NCAR/openiotwx/docs/img/architecture.png

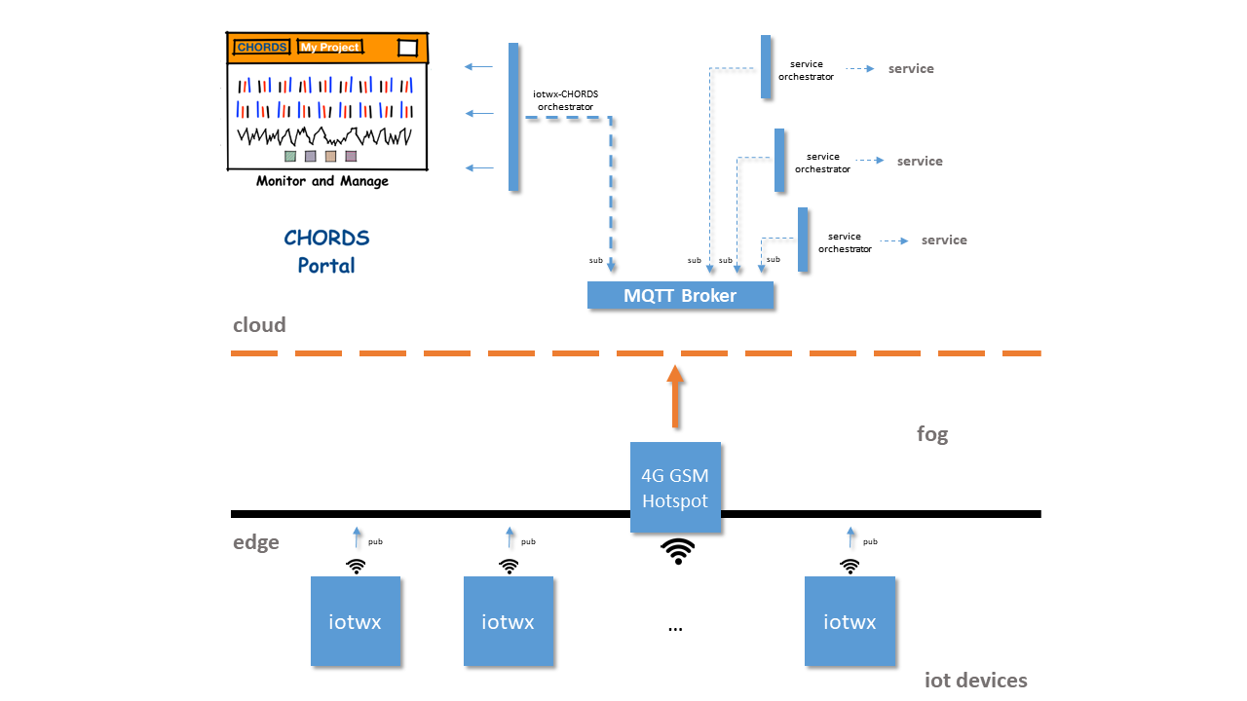
docs/img/architecture.png
