NCAR/openiotwx/docs/img/electronic_layout.png

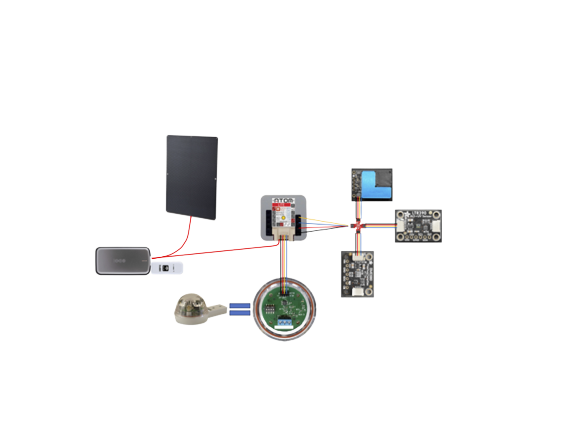
docs/img/electronic_layout.png
