NCAR/openiotwx/docs/sensor_pngs/battery.png

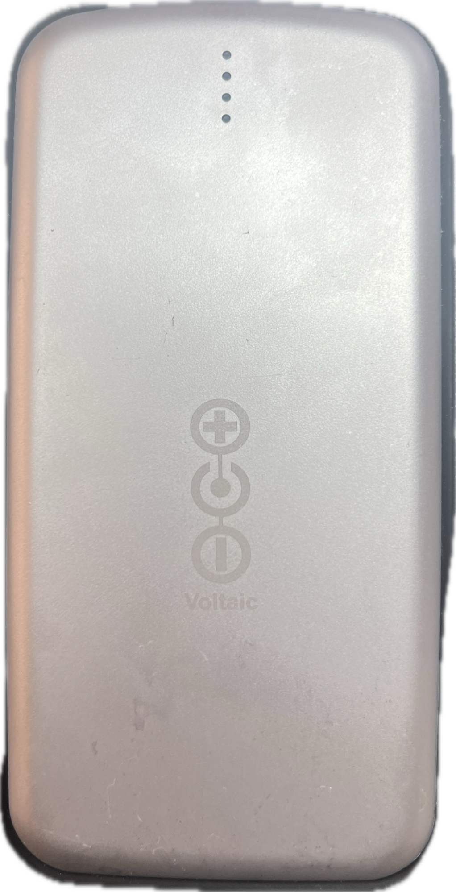
docs/sensor_pngs/battery.png
