NCAR/openiotwx/docs/sensor_pngs/modem.png

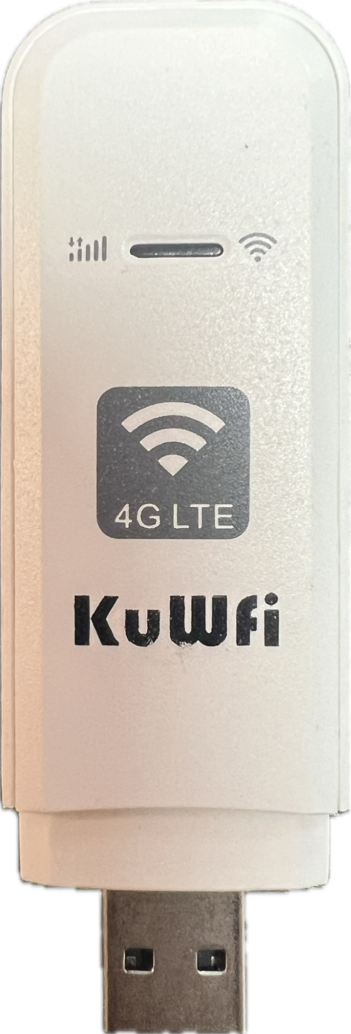
docs/sensor_pngs/modem.png
