NCAR/openiotwx/docs/stl_pngs/AQ_cap.png

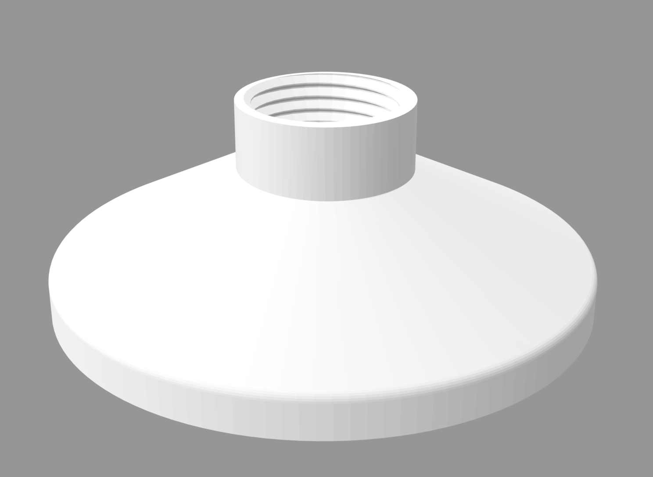
docs/stl_pngs/AQ_cap.png
