NCAR/openiotwx/docs/stl_pngs/AQ_lidlock.png

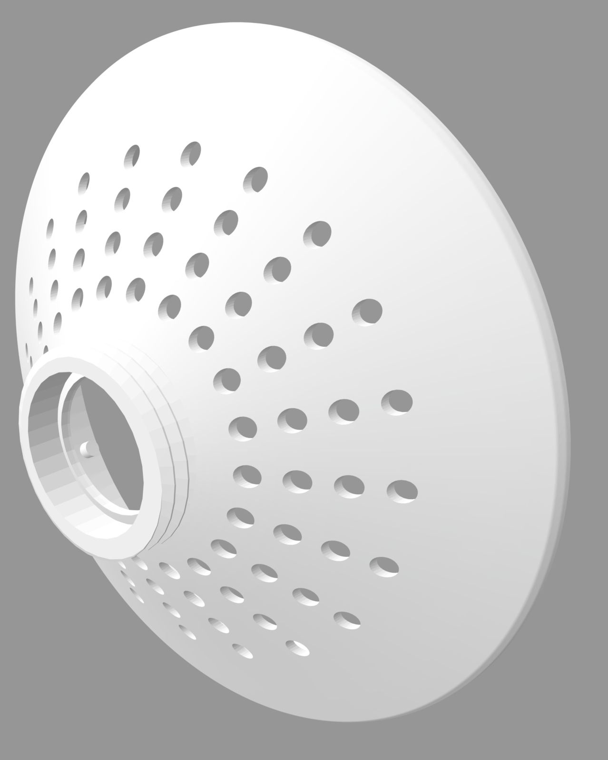
docs/stl_pngs/AQ_lidlock.png
