NCAR/openiotwx/docs/build_img/aq_parts.jpg

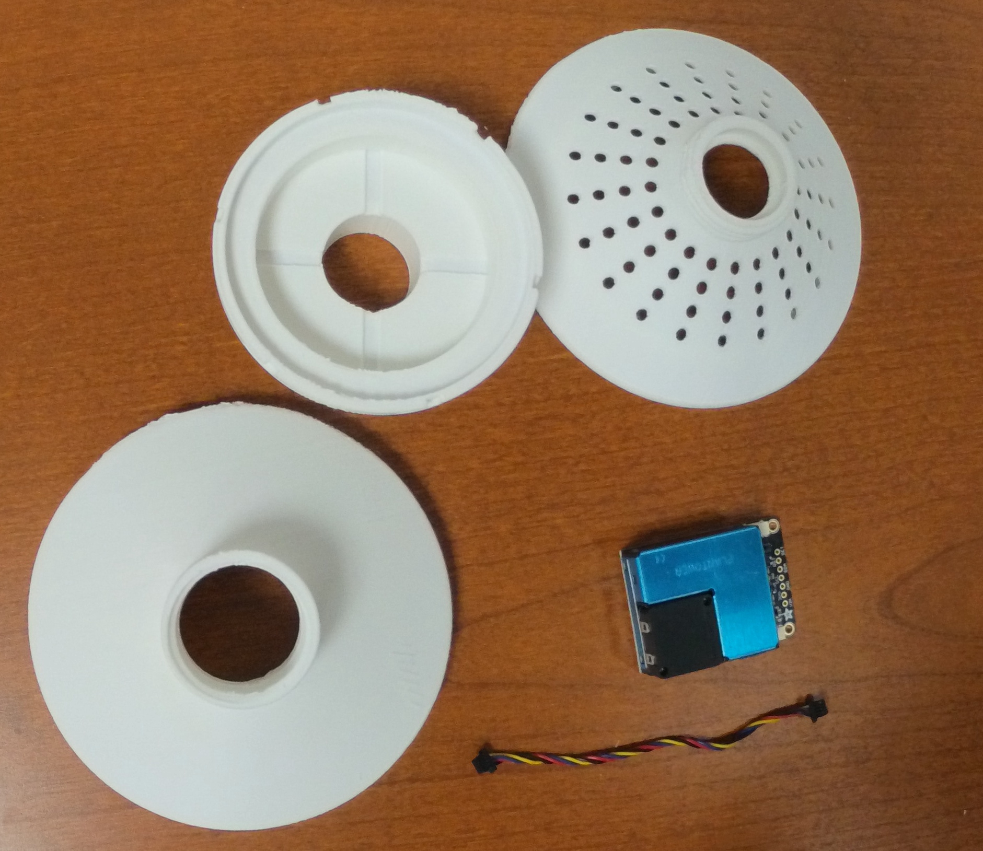
docs/build_img/aq_parts.jpg
