NCAR/openiotwx/docs/build_img/rg_parts.jpg

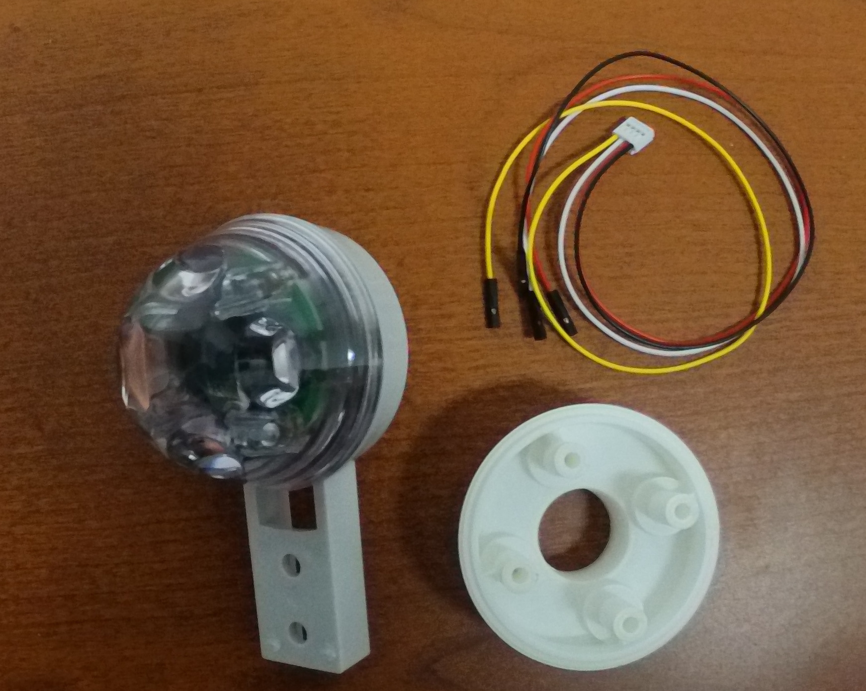
docs/build_img/rg_parts.jpg
