NCAR/openiotwx/docs/build_img/uv_parts.jpg

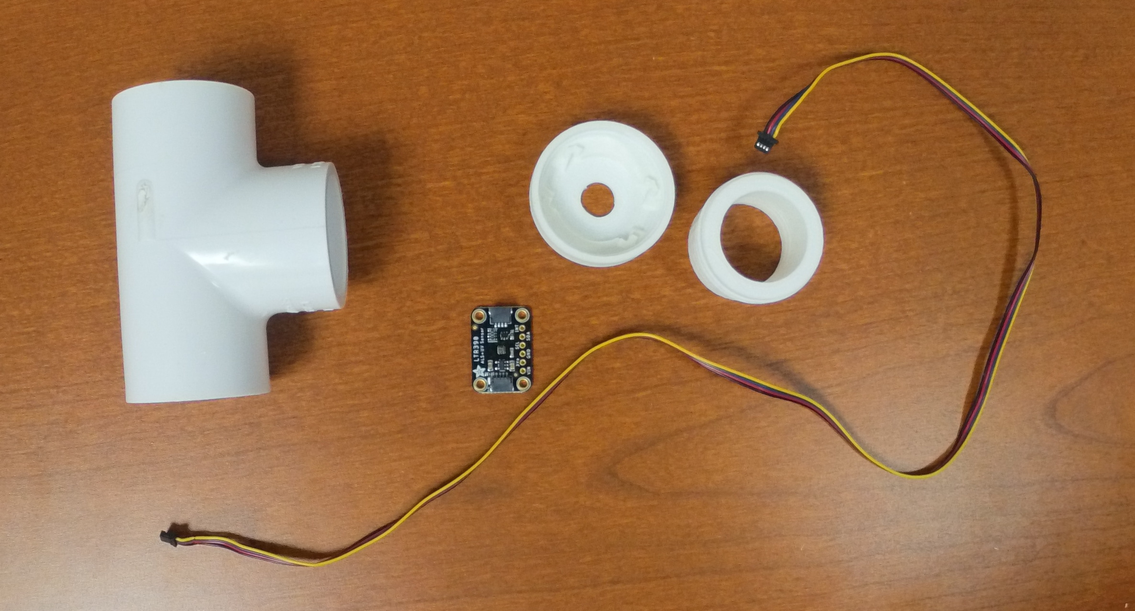
docs/build_img/uv_parts.jpg
