NCAR/openiotwx/material/assets/images/global.png

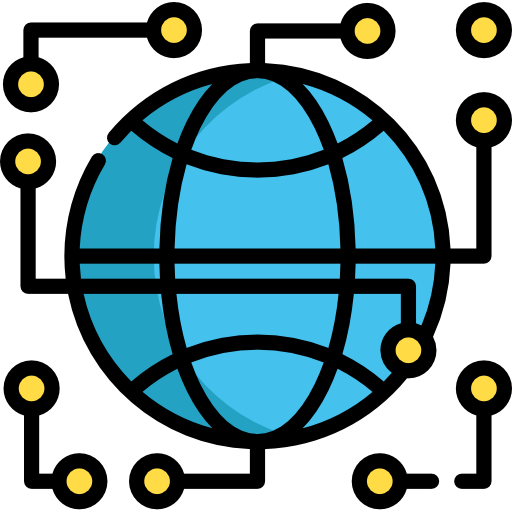
material/assets/images/global.png
