NCAR/openiotwx/docs/print_files/caps/Cap_Open.stl

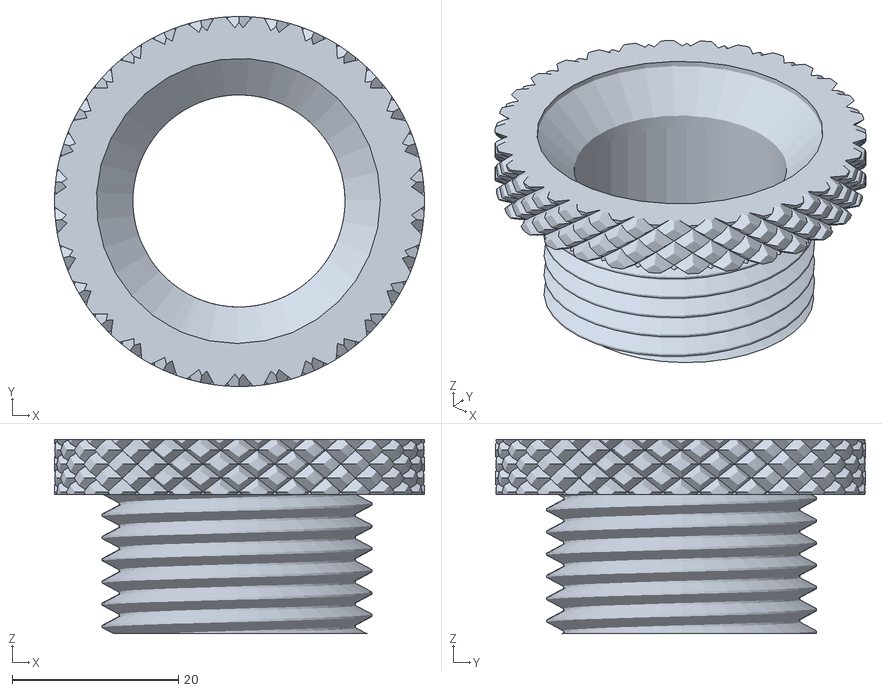
[picture p36: CAD file, 2023-06-20]
docs/print_files/caps/Cap_Open.stl
44.5 x 44.5 x 23.4
