NCAR/openiotwx/docs/print_files/air_quality/AQ_Housing_Male.stl

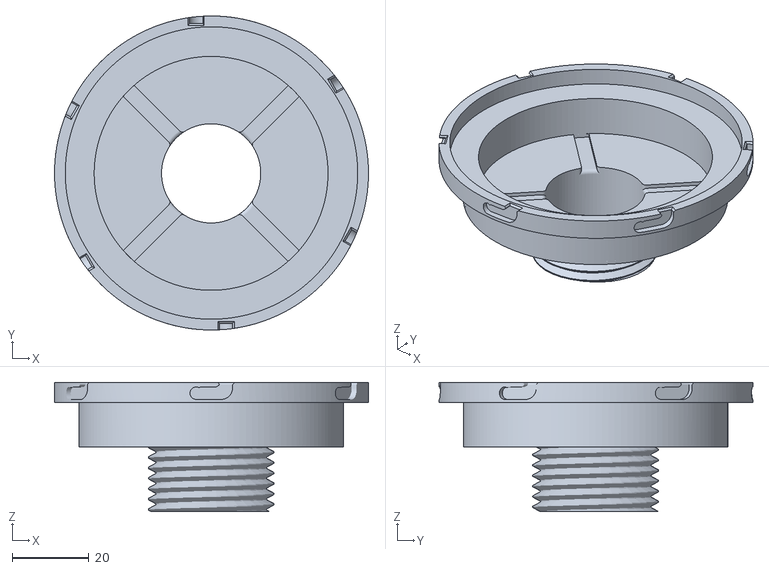
[picture p37: CAD file, 2023-06-16]
docs/print_files/air_quality/AQ_Housing_Male.stl
81.9 x 81.9 x 33.7
