NCAR/openiotwx/docs/assembly_imgs/BME_housing.png

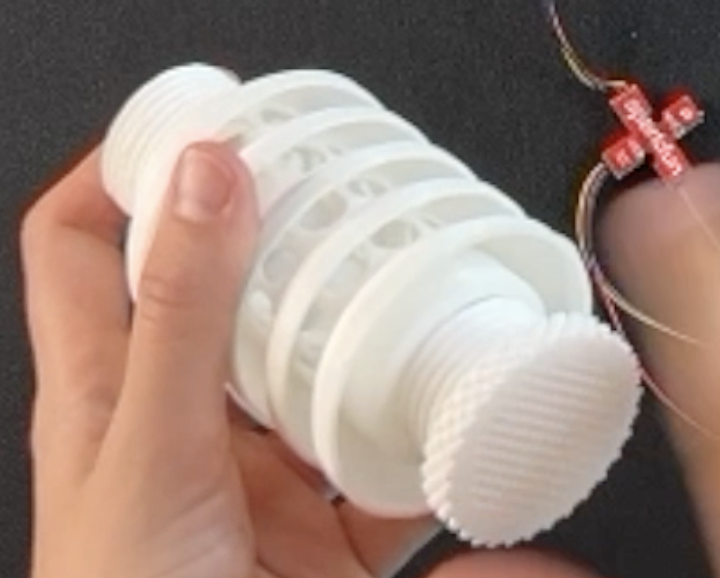
docs/assembly_imgs/BME_housing.png
