NCAR/openiotwx/docs/assembly_imgs/jbox_mounted.png

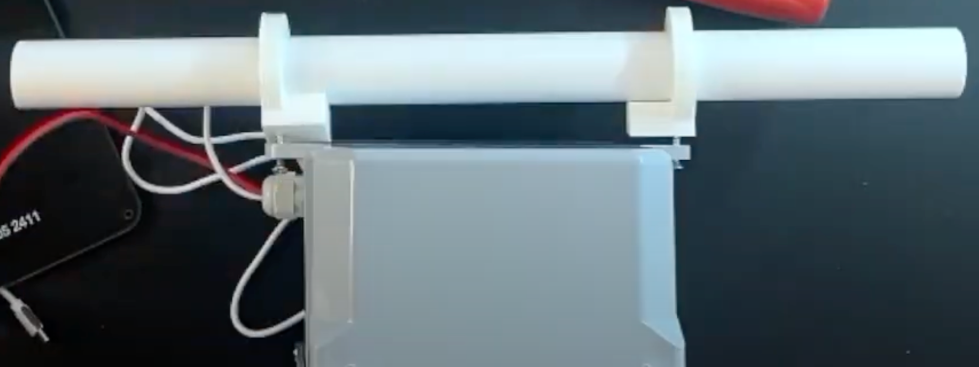
docs/assembly_imgs/jbox_mounted.png
