NCAR/openiotwx/docs/assembly_imgs/microcontroller_wiring.png

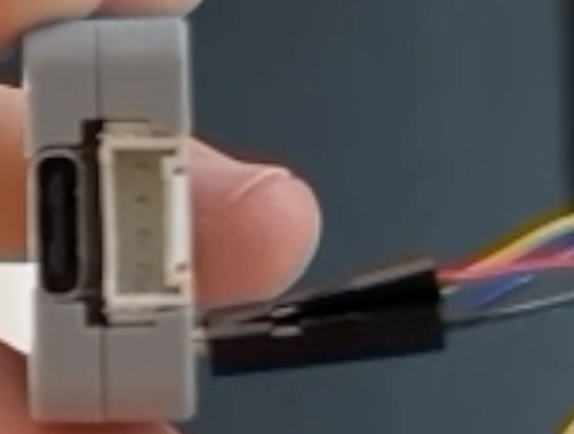
docs/assembly_imgs/microcontroller_wiring.png
