NCAR/openiotwx/docs/assembly_imgs/UV_PVC.png

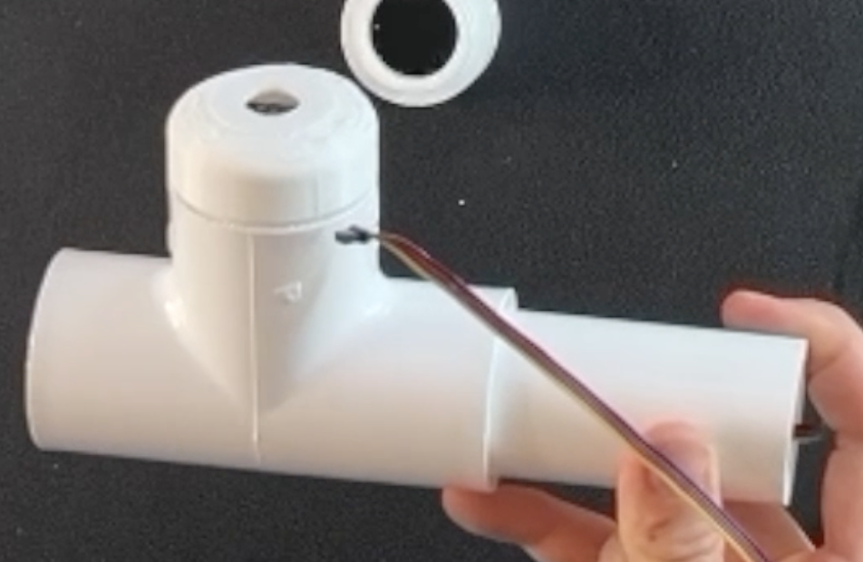
docs/assembly_imgs/UV_PVC.png
