NCAR/openiotwx/docs/assembly_imgs/UV_T_pipe.png

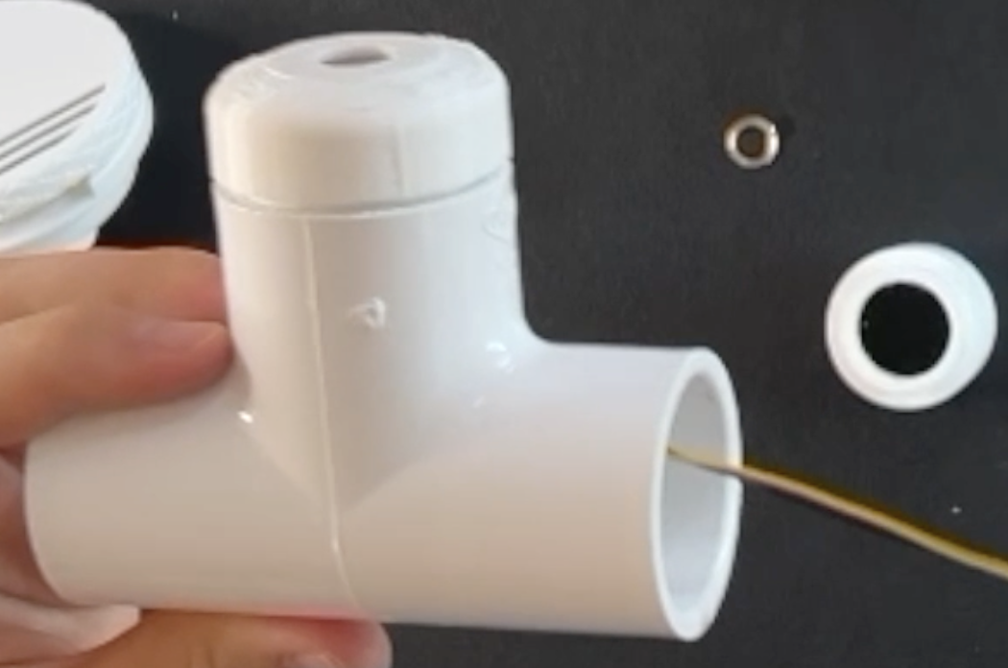
docs/assembly_imgs/UV_T_pipe.png
