NCAR/openiotwx/docs/build_img/aq_built.jpg

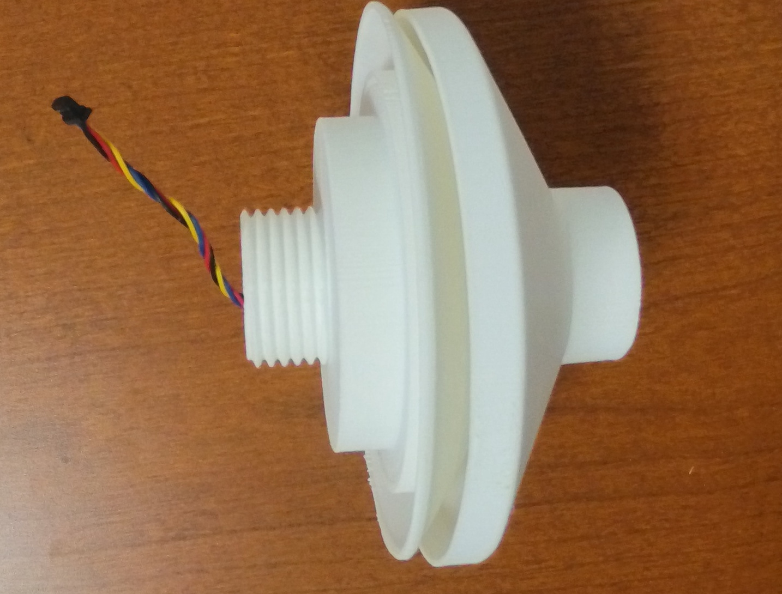
docs/build_img/aq_built.jpg
