NCAR/openiotwx/docs/build_img/aq_process.jpg

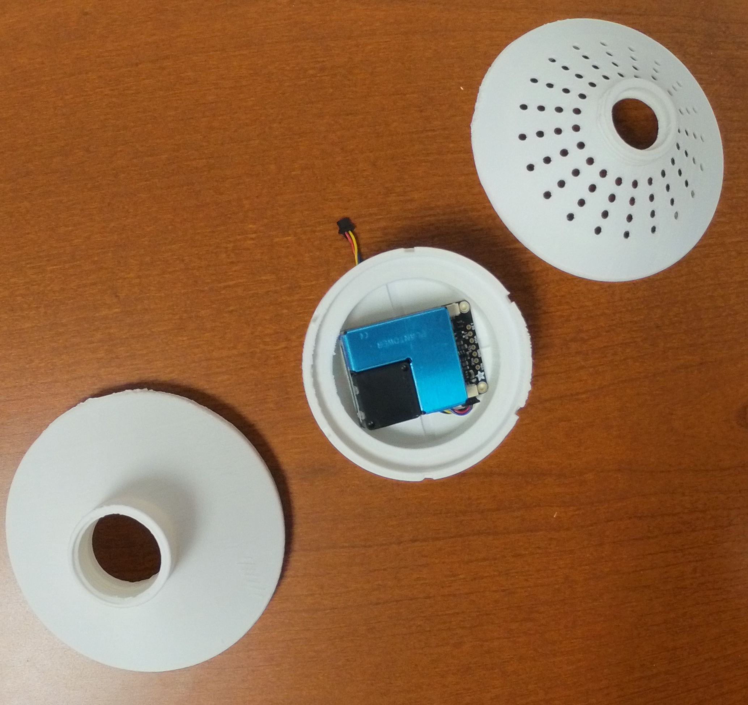
docs/build_img/aq_process.jpg
