NCAR/openiotwx/docs/build_img/charging.jpg

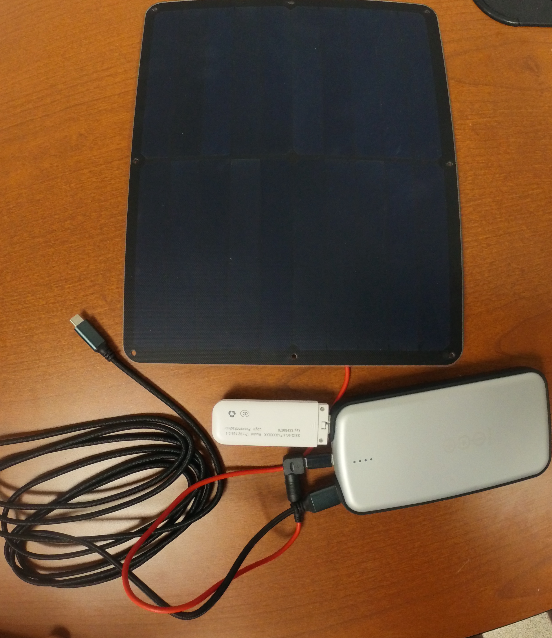
docs/build_img/charging.jpg
