NCAR/openiotwx/docs/build_img/full_station.jpg

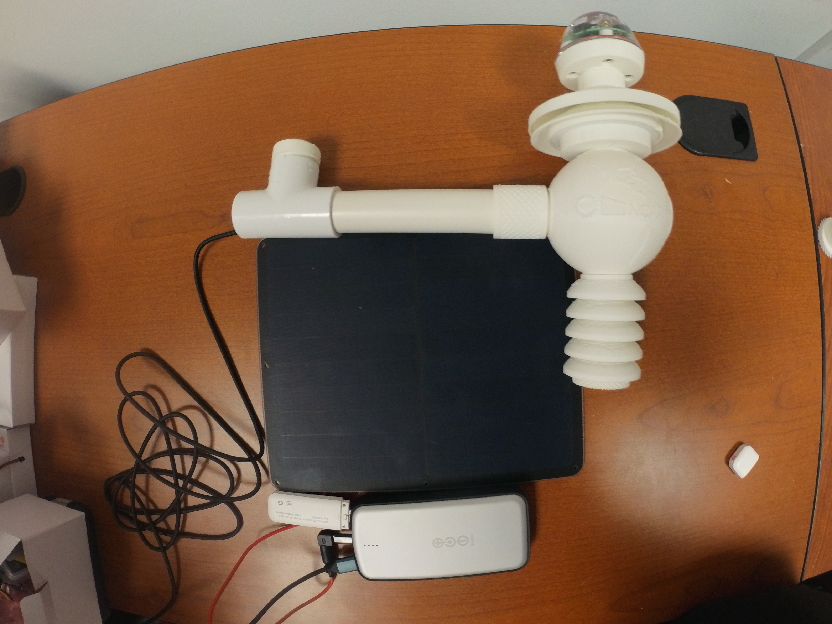
docs/build_img/full_station.jpg
