NCAR/openiotwx/docs/build_img/I2C_front.jpg

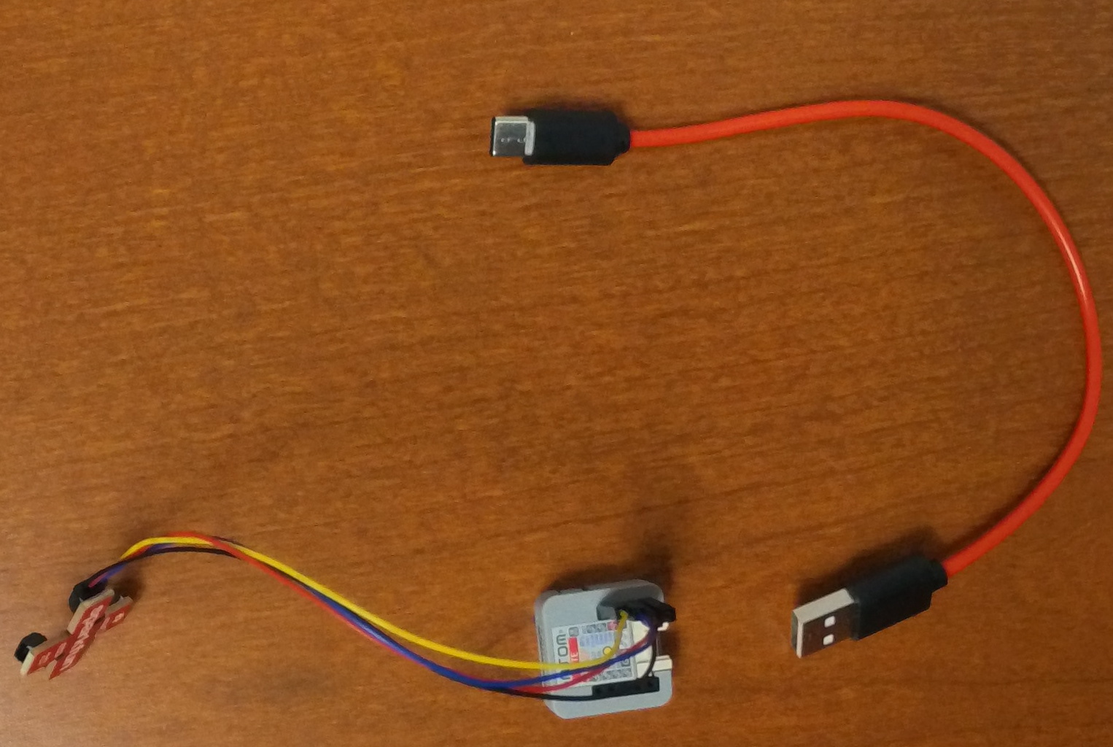
docs/build_img/I2C_front.jpg
