NCAR/openiotwx/docs/build_img/I2C_wiring.jpg

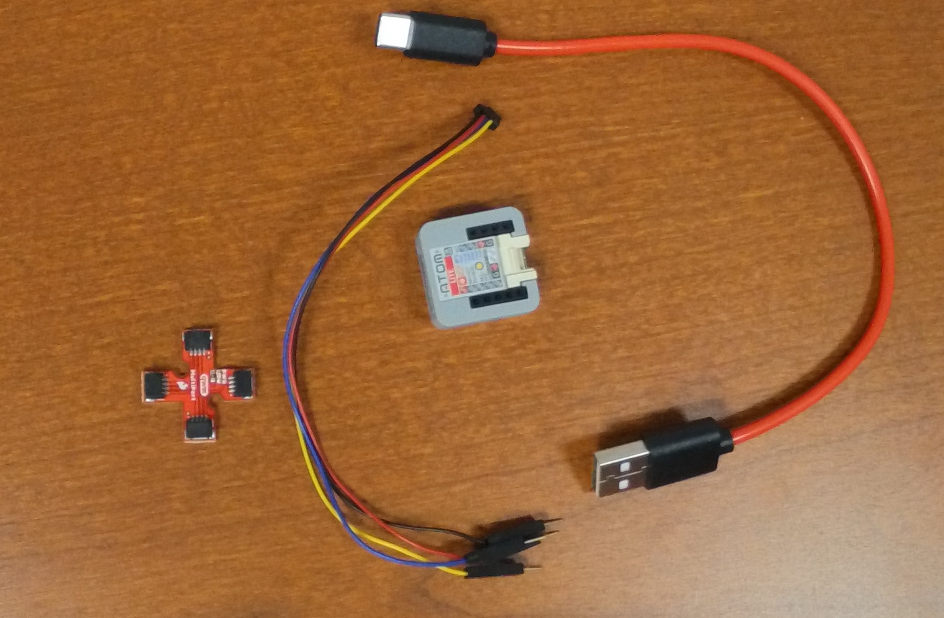
docs/build_img/I2C_wiring.jpg
