NCAR/openiotwx/docs/build_img/orb_rg_aq.jpg

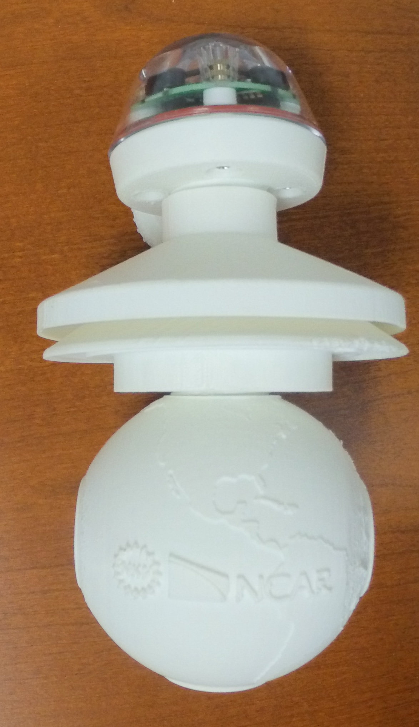
docs/build_img/orb_rg_aq.jpg
