NCAR/openiotwx/docs/build_img/orb_rg_aq_process.jpg

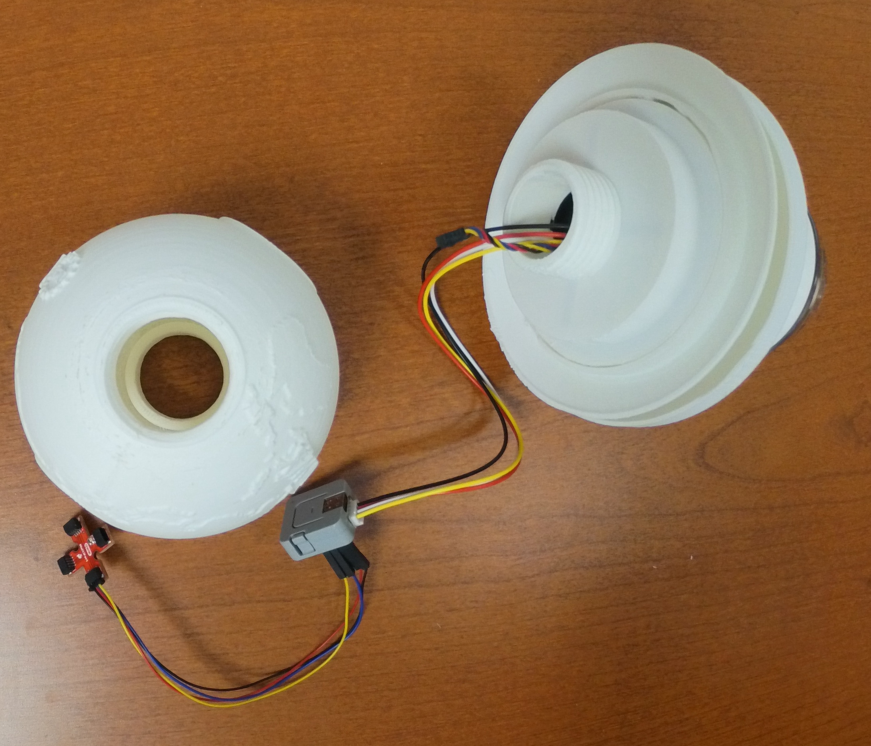
docs/build_img/orb_rg_aq_process.jpg
