NCAR/openiotwx/docs/build_img/radiation_built.jpg

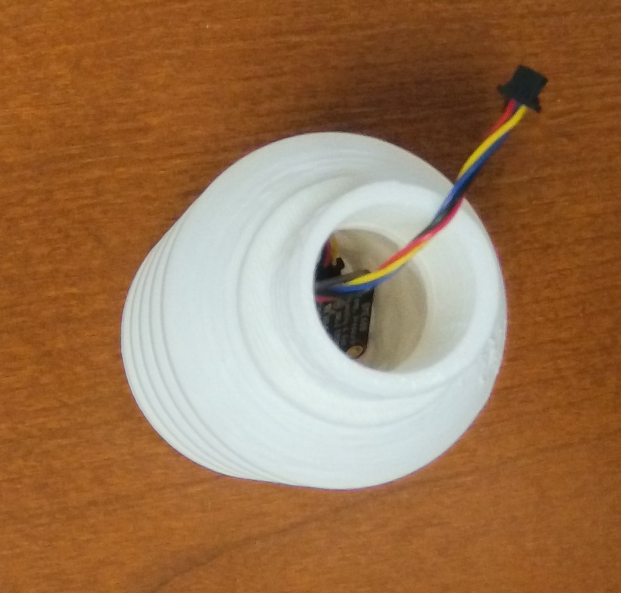
docs/build_img/radiation_built.jpg
