NCAR/openiotwx/docs/build_img/rg_aq_complete.jpg

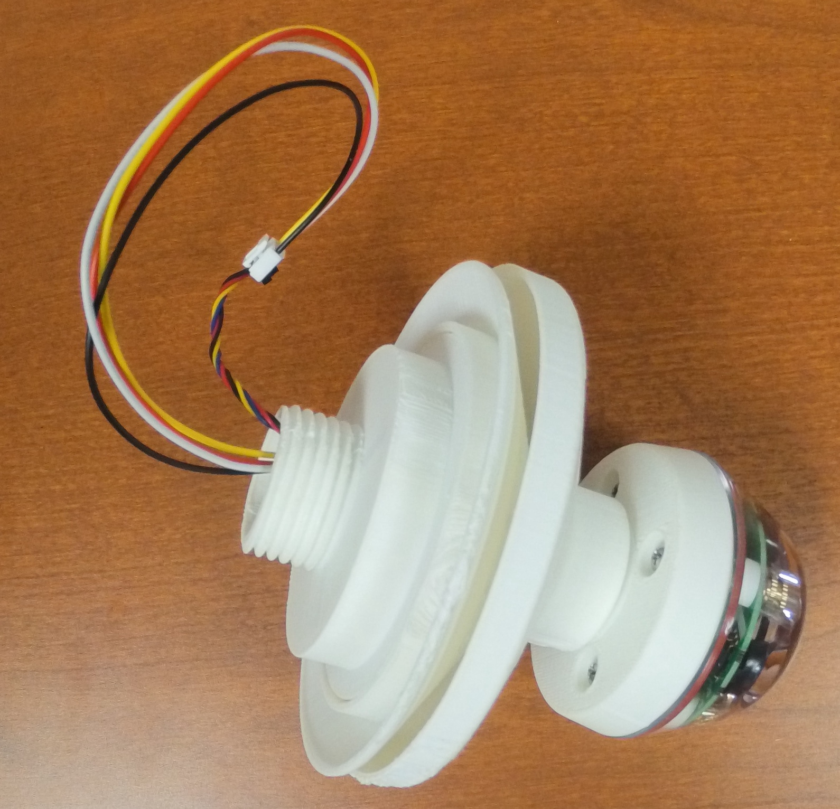
docs/build_img/rg_aq_complete.jpg
