NCAR/openiotwx/docs/build_img/rg_aq_process_0.jpg

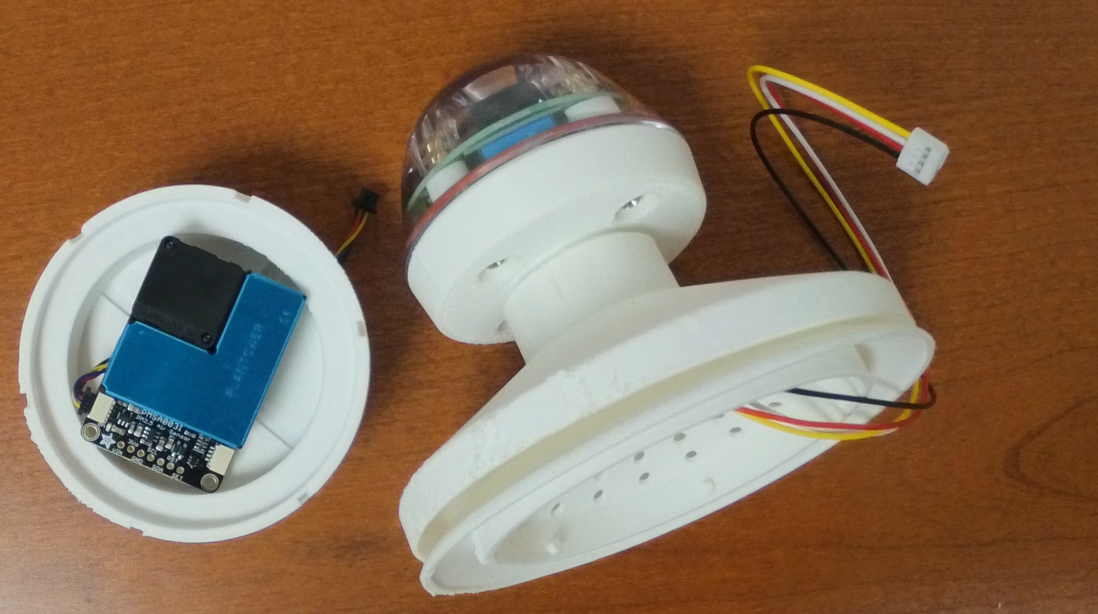
docs/build_img/rg_aq_process_0.jpg
