NCAR/openiotwx/docs/build_img/rg_aq_process_1.jpg

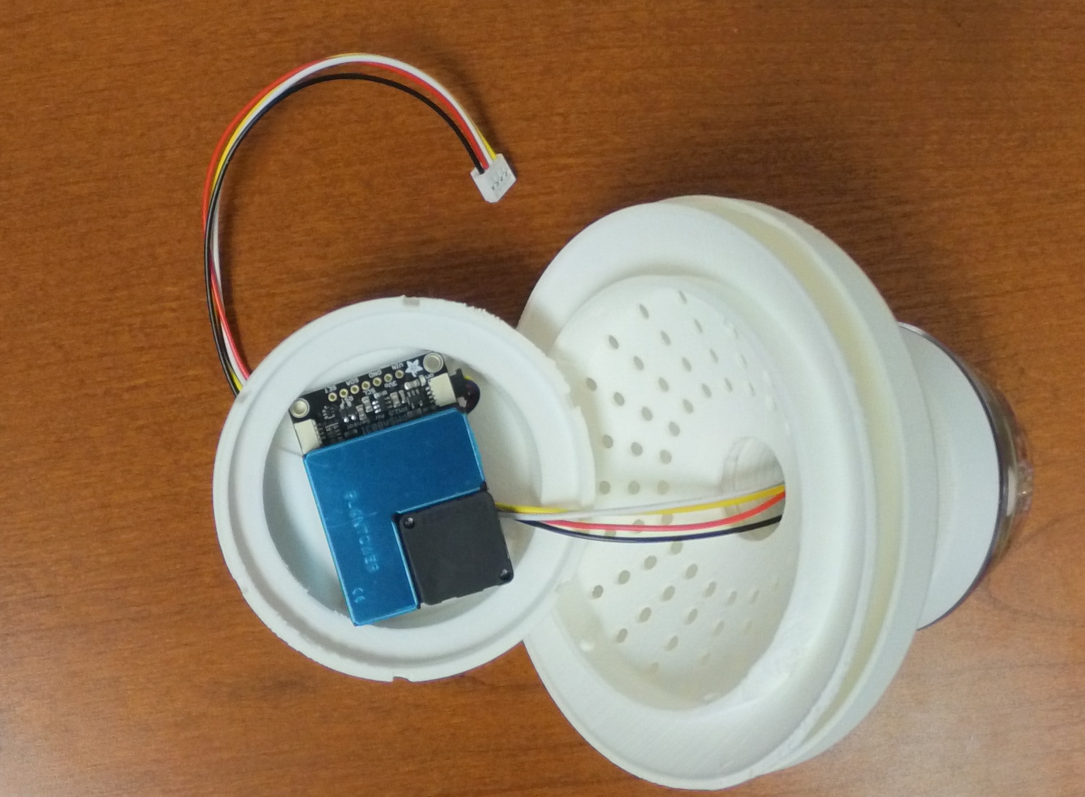
docs/build_img/rg_aq_process_1.jpg
