NCAR/openiotwx/docs/build_img/rg_deconstructed.jpg

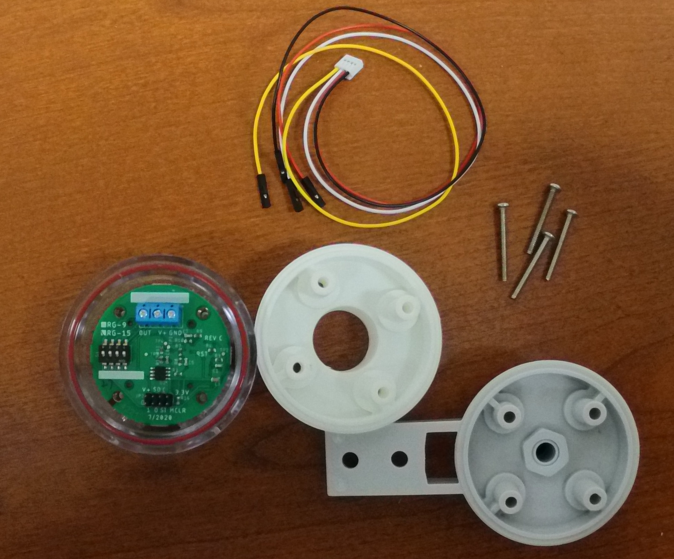
docs/build_img/rg_deconstructed.jpg
