NCAR/openiotwx/docs/build_img/rg_wiring.jpg

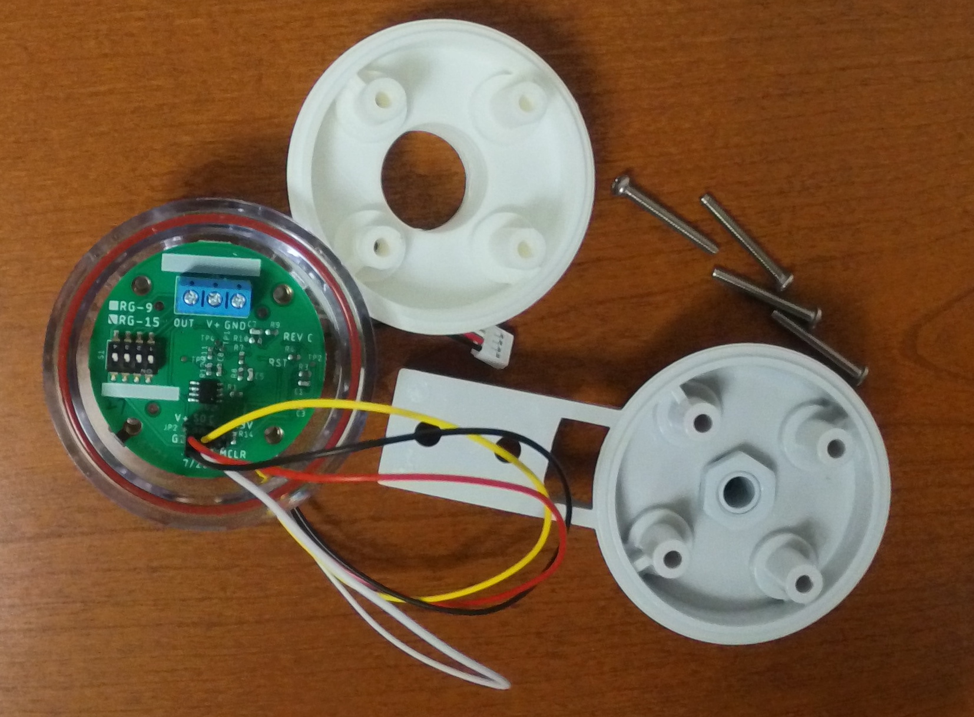
docs/build_img/rg_wiring.jpg
