NCAR/openiotwx/docs/build_img/rg_wiring_detail.jpg

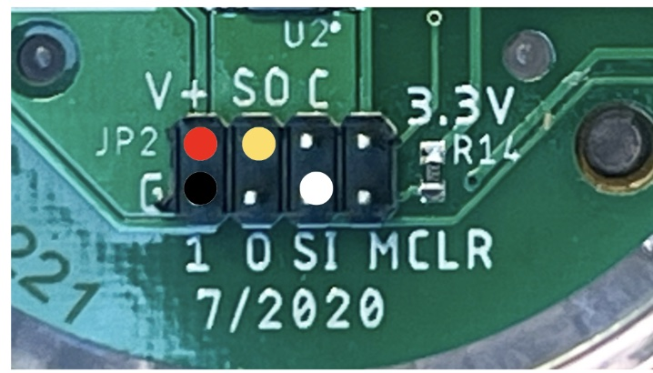
docs/build_img/rg_wiring_detail.jpg
