NCAR/openiotwx/docs/build_img/station_no_power.jpg

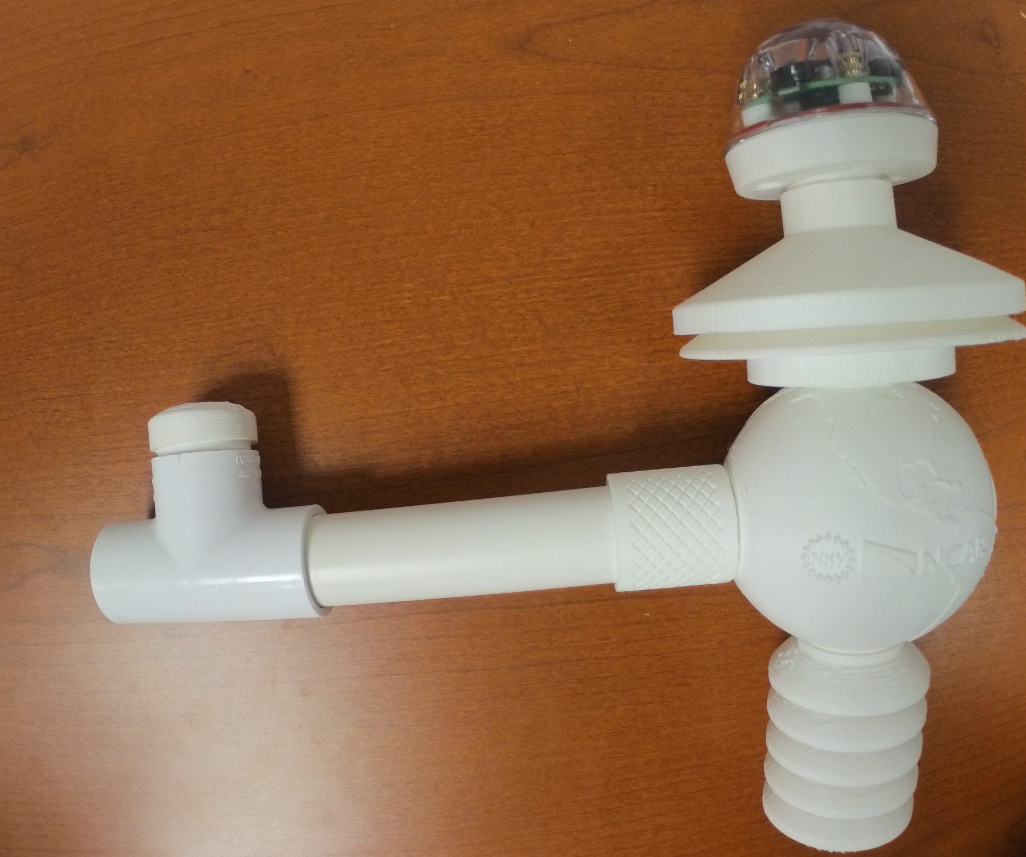
docs/build_img/station_no_power.jpg
