NCAR/openiotwx/docs/build_img/station_no_pvc.jpg

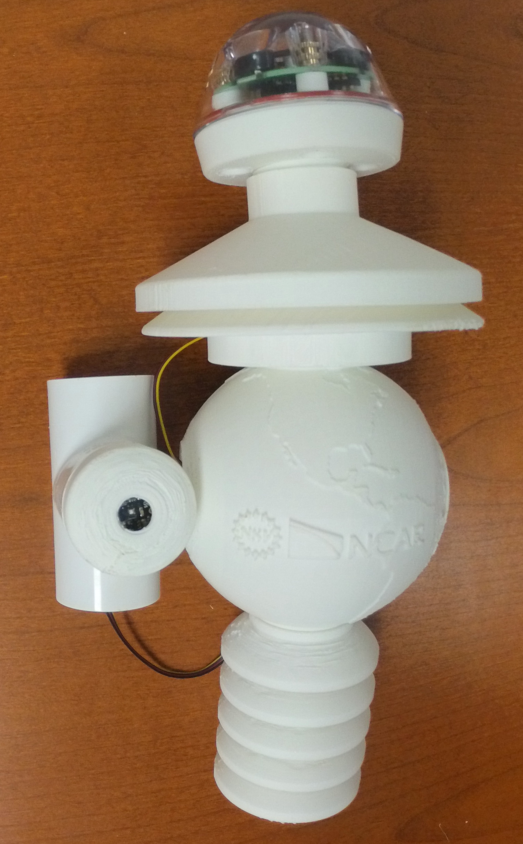
docs/build_img/station_no_pvc.jpg
