NCAR/openiotwx/docs/build_img/uv_complete.jpg

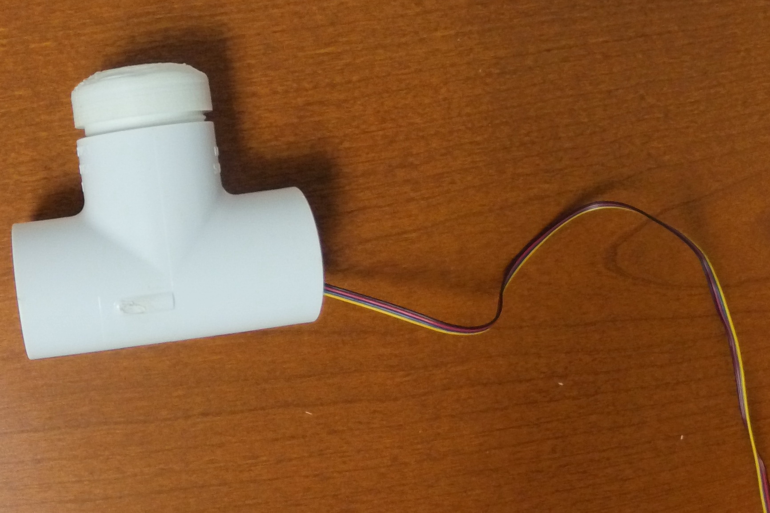
docs/build_img/uv_complete.jpg
