NCAR/openiotwx/docs/build_img/uv_process.jpg

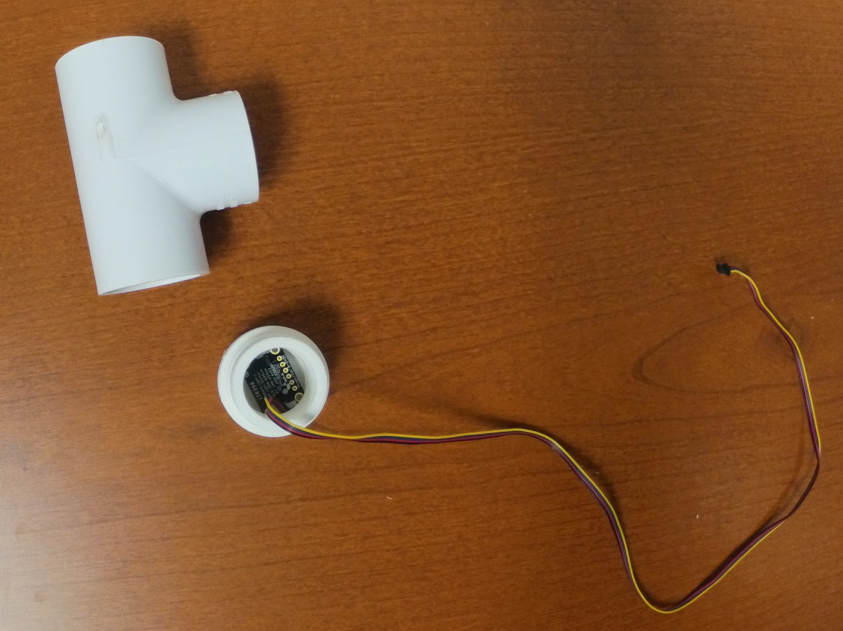
docs/build_img/uv_process.jpg
